Phirks/flip-card/kicad-pcb/RP2350_60QFN_minimal.kicad_sch

## KiCad design kicad-pcb/RP2350_60QFN_minimal.kicad_sch (2025-08-04)

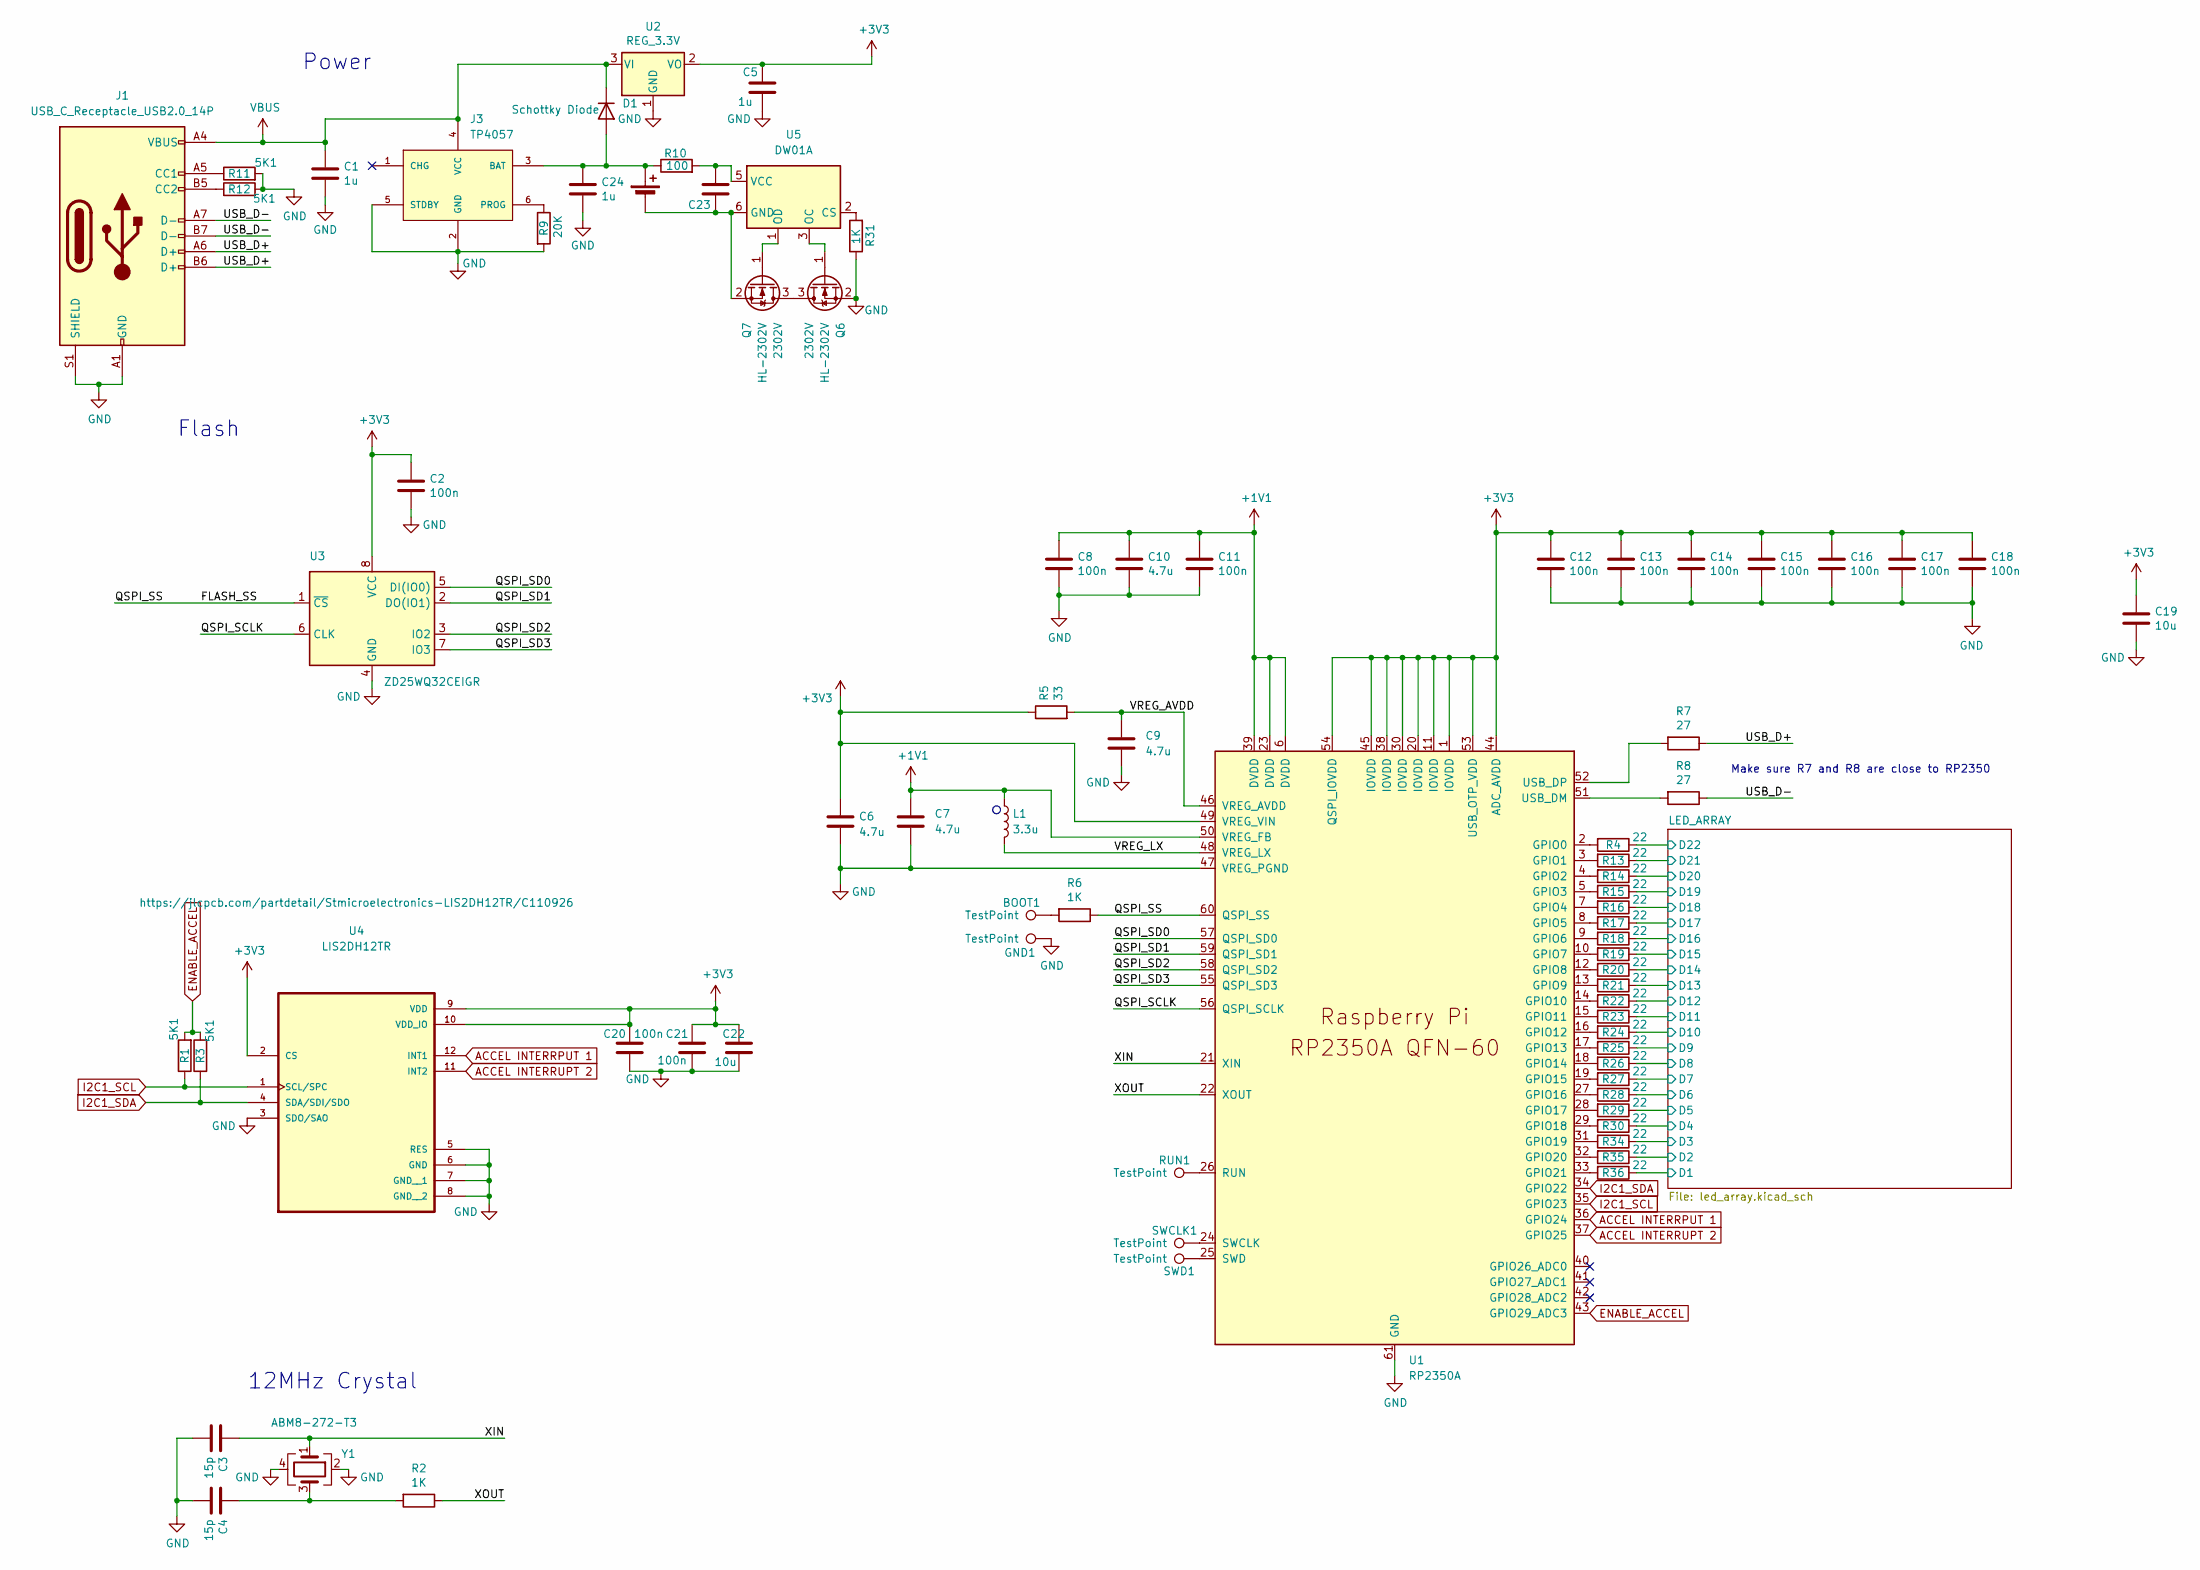
[picture p12: schematic RP2350_60QFN_minimal.kicad_sch]

Parts:
BOOT1: TestPoint; TestPoint_Pad_1.0x1.0mm
BT1: Battery_Cell; BatteryHolder_Custom; Part Number RJD2430C1ST1
C1, C5, C24: 1u; C_0402_1005Metric_small_pads; Part Number TCC0402X5R105M6R3AT
C2, C8, C11, C12, C13, C14, C15, C16, C17, C18, C20, C21, C23: 100n; C_0402_1005Metric_small_pads; Part Number FCC0402B104K160AT
C3, C4: 15p; C_0402_1005Metric_small_pads; Part Number CC0402FRNPO9BN150
C6, C7, C9, C10: 4.7u; C_0402_1005Metric_small_pads; Part Number TCC0402X5R475M6R3AT
C19, C22: 10u; C_0402_1005Metric_small_pads; Part Number GRM155R60J106ME44D
D1: Schottky Diode; D_SOD-323; Part Number CUS10S30,H3F; JLC Number C146335
GND1: TestPoint; TestPoint_Pad_1.0x1.0mm
J1: USB_C_Receptacle_USB2.0_14P; USB_C_PADDLE
J3: TP4057; SOT-23-6; Part Number TP4057; LCSC Part Number C497923
L1: 3.3u; L_pol_2016; Part Number AOTA-B201610S3R3-101-T
Q6, Q7: HL-2302V; SOT-23; Part Number 2302V; LCSC Part Number C7431443
R1, R3, R11, R12: 5K1; R_0402_1005Metric; Part Number 0402WGF510KTCE
R2, R6, R31: 1K; R_0402_1005Metric; Part Number FRC0402F1001TS
R4, R13, R14, R15, R16, R17, R18, R19, R20, R21, R22, R23, R24, R25, R26, R27, R28, R29, R30, R34, R35, R36: 22; R_0402_1005Metric; Part Number 0402WGF220JTCE
R5: 33; R_0402_1005Metric; Part Number RC0402FR-0733RL
R7, R8: 27; R_0402_1005Metric; Part Number 0402WGJ0100TCE
R9: 20K; R_0402_1005Metric; Part Number 0402WGF2002TCE
R10: 100; R_0402_1005Metric; Part Number FRC0402F1000TS
RUN1: TestPoint; TestPoint_Pad_1.0x1.0mm
SWCLK1: TestPoint; TestPoint_Pad_1.0x1.0mm
SWD1: TestPoint; TestPoint_Pad_1.0x1.0mm
U1: RP2350A; RP2350-QFN-60-1EP_7x7_P0.4mm_EP3.4x3.4mm_ThermalVias; Part Number RP2350A
U2: REG_3.3V; SOT-23; Part Number XC6206P332MR-MS
U3: ZD25WQ32CEIGR; Winbond_USON-8-1EP_3x2mm_P0.5mm_EP0.2x1.6mm; Part Number ZD25WQ32CEIGR
U4: LIS2DH12TR; LGA-12_2x2mm_P0.5mm; Part Number LIS2DH12TR
U5: DW01A; SOT-23-6; Part Number DW01A; LCSC Part Number C42380662
Y1: ABM8-272-T3; Crystal_SMD_3225-4Pin_3.2x2.5mm

Connections:
+1V1: C7.1, C8.1, C10.1, C11.1, L1.1, U1.6 (DVDD), U1.23 (DVDD), U1.39 (DVDD), U1.50 (VREG_FB)
+3V3: C2.1, C5.1, C6.1, C12.1, C13.1, C14.1, C15.1, C16.1, C17.1, C18.1, C19.1, C20.2, C21.2, C22.1, R5.1, U1.1 (IOVDD), U1.11 (IOVDD), U1.20 (IOVDD), U1.30 (IOVDD), U1.38 (IOVDD), U1.44 (ADC_AVDD), U1.45 (IOVDD), U1.49 (VREG_VIN), U1.53 (USB_OTP_VDD), U1.54 (QSPI_IOVDD), U2.2 (VO), U3.8 (VCC), U4.2 (CS), U4.9 (VDD), U4.10 (VDD_IO)
ACCEL INTERRPUT 1: U1.36 (GPIO24), U4.12 (INT1)
ACCEL INTERRUPT 2: U1.37 (GPIO25), U4.11 (INT2)
D1: R36.1
D2: R35.1
D3: R34.1
D4: R30.1
D5: R29.1
D6: R28.1
D7: R27.1
D8: R26.1
D9: R25.1
D10: R24.1
D11: R23.1
D12: R22.1
D13: R21.1
D14: R20.1
D15: R19.1
D16: R18.1
D17: R17.1
D18: R16.1
D19: R15.1
D20: R14.1
D21: R13.1
D22: R4.1
ENABLE_ACCEL: R1.2, R3.2, U1.43 (GPIO29_ADC3)
FLASH_SS: R6.1, U1.60 (QSPI_SS), U3.1 (~CS)
GND: C1.2, C2.2, C3.2, C4.2, C5.2, C6.2, C7.2, C8.2, C9.2, C10.2, C11.2, C12.2, C13.2, C14.2, C15.2, C16.2, C17.2, C18.2, C19.2, C20.1, C21.1, C22.2, C24.2, GND1.1, J1.A1 (GND), J1.A12 (GND), J1.B1 (GND), J1.B12 (GND), J1.S1 (SHIELD), J3.2 (GND), J3.5 (STDBY), Q6.2 (S), R9.2, R11.2, R12.2, R31.1, U1.47 (VREG_PGND), U1.61 (GND), U2.1 (GND), U3.4 (GND), U4.3 (SDO/SAO), U4.5 (RES), U4.6 (GND), U4.7 (GND__1), U4.8 (GND__2), Y1.2, Y1.4
I2C1_SCL: R1.1, U1.35 (GPIO23), U4.1 (SCL/SPC)
I2C1_SDA: R3.1, U1.34 (GPIO22), U4.4 (SDA/SDI/SDO)
unnamed: BOOT1.1, R6.2
unnamed: BT1.1 (+), C24.1, D1.2 (A), J3.3 (BAT), R10.1
unnamed: BT1.2 (-), C23.2, Q7.2 (S), U5.6 (GND)
unnamed: C4.1, R2.2, Y1.3
unnamed: C23.1, R10.2, U5.5 (VCC)
unnamed: J1.A5 (CC1), R11.1
unnamed: J1.B5 (CC2), R12.1
unnamed: J3.6 (PROG), R9.1
unnamed: Q6.1 (G), U5.3 (OC)
unnamed: Q6.3 (D), Q7.3 (D)
unnamed: Q7.1 (G), U5.1 (OD)
unnamed: R4.2, U1.2 (GPIO0)
unnamed: R7.2, U1.52 (USB_DP)
unnamed: R8.2, U1.51 (USB_DM)
unnamed: R13.2, U1.3 (GPIO1)
unnamed: R14.2, U1.4 (GPIO2)
unnamed: R15.2, U1.5 (GPIO3)
unnamed: R16.2, U1.7 (GPIO4)
unnamed: R17.2, U1.8 (GPIO5)
unnamed: R18.2, U1.9 (GPIO6)
unnamed: R19.2, U1.10 (GPIO7)
unnamed: R20.2, U1.12 (GPIO8)
unnamed: R21.2, U1.13 (GPIO9)
unnamed: R22.2, U1.14 (GPIO10)
unnamed: R23.2, U1.15 (GPIO11)
unnamed: R24.2, U1.16 (GPIO12)
unnamed: R25.2, U1.17 (GPIO13)
unnamed: R26.2, U1.18 (GPIO14)
unnamed: R27.2, U1.19 (GPIO15)
unnamed: R28.2, U1.27 (GPIO16)
unnamed: R29.2, U1.28 (GPIO17)
unnamed: R30.2, U1.29 (GPIO18)
unnamed: R31.2, U5.2 (CS)
unnamed: R34.2, U1.31 (GPIO19)
unnamed: R35.2, U1.32 (GPIO20)
unnamed: R36.2, U1.33 (GPIO21)
unnamed: RUN1.1, U1.26 (RUN)
unnamed: SWCLK1.1, U1.24 (SWCLK)
unnamed: SWD1.1, U1.25 (SWD)
QSPI_SCLK: U1.56 (QSPI_SCLK), U3.6 (CLK)
QSPI_SD0: U1.57 (QSPI_SD0), U3.5 (DI(IO0))
QSPI_SD1: U1.59 (QSPI_SD1), U3.2 (DO(IO1))
QSPI_SD2: U1.58 (QSPI_SD2), U3.3 (IO2)
QSPI_SD3: U1.55 (QSPI_SD3), U3.7 (IO3)
USB_D+: J1.A6 (D+), J1.B6 (D+), R7.1
USB_D-: J1.A7 (D-), J1.B7 (D-), R8.1
VBUS: C1.1, D1.1 (K), J1.A4 (VBUS), J1.A9 (VBUS), J1.B4 (VBUS), J1.B9 (VBUS), J3.4 (VCC), U2.3 (VI)
VREG_AVDD: C9.1, R5.2, U1.46 (VREG_AVDD)
VREG_LX: L1.2, U1.48 (VREG_LX)
XIN: C3.1, U1.21 (XIN), Y1.1
XOUT: R2.1, U1.22 (XOUT)

Notes on the sheet:
Flash
Make sure R7 and R8 are close to RP2350
12MHz Crystal
Power
