Phirks/flip-card/kicad-pcb/led_array.kicad_sch

## KiCad design kicad-pcb/led_array.kicad_sch (2025-08-04)

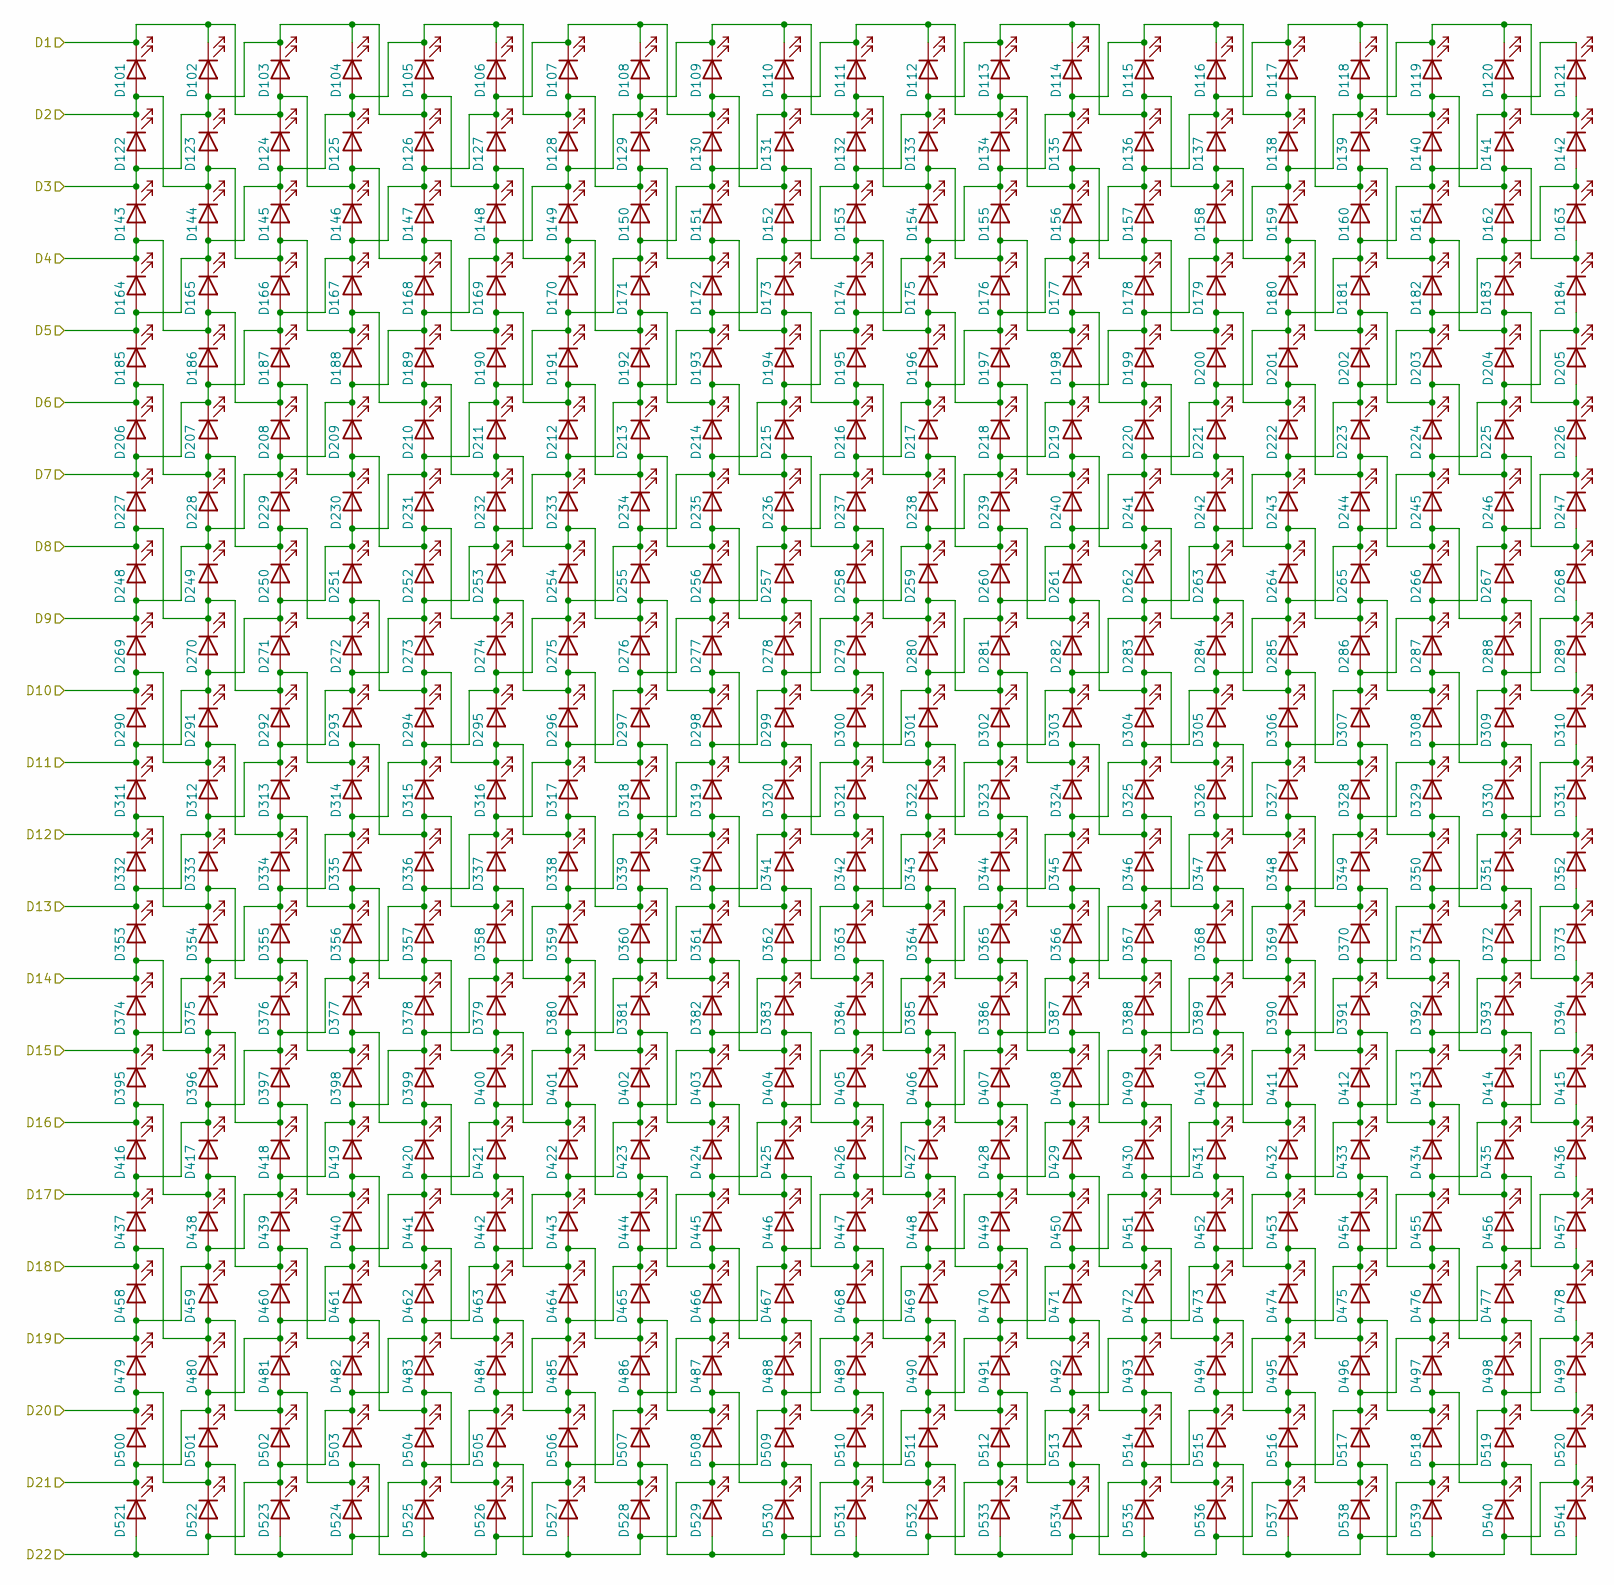
[picture p13: schematic led_array.kicad_sch]

Parts:
D101, D102, D103, D104, D105, D106, D107, D108, D109, D110, D111, D112, D113, D114, D115, D116, D117, D118, D119, D120, D121, D122, D123, D124, D125, D126, D127, D128, D129, D130, D131, D132, D133, D134, D135, D136, D137, D138, D139, D140, D141, D142, D143, D144, D145, D146, D147, D148, D149, D150, D151, D152, D153, D154, D155, D156, D157, D158, D159, D160, D161, D162, D163, D164, D165, D166, D167, D168, D169, D170, D171, D172, D173, D174, D175, D176, D177, D178, D179, D180, D181, D182, D183, D184, D185, D186, D187, D188, D189, D190, D191, D192, D193, D194, D195, D196, D197, D198, D199, D200, D201, D202, D203, D204, D205, D206, D207, D208, D209, D210, D211, D212, D213, D214, D215, D216, D217, D218, D219, D220, D221, D222, D223, D224, D225, D226, D227, D228, D229, D230, D231, D232, D233, D234, D235, D236, D237, D238, D239, D240, D241, D242, D243, D244, D245, D246, D247, D248, D249, D250, D251, D252, D253, D254, D255, D256, D257, D258, D259, D260, D261, D262, D263, D264, D265, D266, D267, D268, D269, D270, D271, D272, D273, D274, D275, D276, D277, D278, D279, D280, D281, D282, D283, D284, D285, D286, D287, D288, D289, D290, D291, D292, D293, D294, D295, D296, D297, D298, D299, D300, D301, D302, D303, D304, D305, D306, D307, D308, D309, D310, D311, D312, D313, D314, D315, D316, D317, D318, D319, D320, D321, D322, D323, D324, D325, D326, D327, D328, D329, D330, D331, D332, D333, D334, D335, D336, D337, D338, D339, D340, D341, D342, D343, D344, D345, D346, D347, D348, D349, D350, D351, D352, D353, D354, D355, D356, D357, D358, D359, D360, D361, D362, D363, D364, D365, D366, D367, D368, D369, D370, D371, D372, D373, D374, D375, D376, D377, D378, D379, D380, D381, D382, D383, D384, D385, D386, D387, D388, D389, D390, D391, D392, D393, D394, D395, D396, D397, D398, D399, D400, D401, D402, D403, D404, D405, D406, D407, D408, D409, D410, D411, D412, D413, D414, D415, D416, D417, D418, D419, D420, D421, D422, D423, D424, D425, D426, D427, D428, D429, D430, D431, D432, D433, D434, D435, D436, D437, D438, D439, D440, D441, D442, D443, D444, D445, D446, D447, D448, D449, D450, D451, D452, D453, D454, D455, D456, D457, D458, D459, D460, D461, D462, D463, D464, D465, D466, D467, D468, D469, D470, D471, D472, D473, D474, D475, D476, D477, D478, D479, D480, D481, D482, D483, D484, D485, D486, D487, D488, D489, D490, D491, D492, D493, D494, D495, D496, D497, D498, D499, D500, D501, D502, D503, D504, D505, D506, D507, D508, D509, D510, D511, D512, D513, D514, D515, D516, D517, D518, D519, D520, D521, D522, D523, D524, D525, D526, D527, D528, D529, D530, D531, D532, D533, D534, D535, D536, D537, D538, D539, D540, D541: LED; LED_0603_1608Metric; Part Number HL-PT-1608H322W-L(6000K-7000K)

Connections:
D1: D101.1 (K), D102.1 (K), D103.2 (A), D124.1 (K), D125.2 (A), D146.1 (K), D147.2 (A), D168.1 (K), D169.2 (A), D190.1 (K), D191.2 (A), D212.1 (K), D213.2 (A), D234.1 (K), D235.2 (A), D256.1 (K), D257.2 (A), D278.1 (K), D279.2 (A), D300.1 (K), D301.2 (A), D322.1 (K), D323.2 (A), D344.1 (K), D345.2 (A), D366.1 (K), D367.2 (A), D388.1 (K), D389.2 (A), D410.1 (K), D411.2 (A), D432.1 (K), D433.2 (A), D454.1 (K), D455.2 (A), D476.1 (K), D477.2 (A), D498.1 (K), D499.2 (A), D520.1 (K)
D2: D101.2 (A), D122.1 (K), D123.2 (A), D144.1 (K), D145.2 (A), D166.1 (K), D167.2 (A), D188.1 (K), D189.2 (A), D210.1 (K), D211.2 (A), D232.1 (K), D233.2 (A), D254.1 (K), D255.2 (A), D276.1 (K), D277.2 (A), D298.1 (K), D299.2 (A), D320.1 (K), D321.2 (A), D342.1 (K), D343.2 (A), D364.1 (K), D365.2 (A), D386.1 (K), D387.2 (A), D408.1 (K), D409.2 (A), D430.1 (K), D431.2 (A), D452.1 (K), D453.2 (A), D474.1 (K), D475.2 (A), D496.1 (K), D497.2 (A), D518.1 (K), D519.2 (A), D540.1 (K), D541.2 (A)
D3: D102.2 (A), D103.1 (K), D104.1 (K), D105.2 (A), D122.2 (A), D123.1 (K), D126.1 (K), D127.2 (A), D143.1 (K), D148.1 (K), D149.2 (A), D170.1 (K), D171.2 (A), D192.1 (K), D193.2 (A), D214.1 (K), D215.2 (A), D236.1 (K), D237.2 (A), D258.1 (K), D259.2 (A), D280.1 (K), D281.2 (A), D302.1 (K), D303.2 (A), D324.1 (K), D325.2 (A), D346.1 (K), D347.2 (A), D368.1 (K), D369.2 (A), D390.1 (K), D391.2 (A), D412.1 (K), D413.2 (A), D434.1 (K), D435.2 (A), D456.1 (K), D457.2 (A), D478.1 (K)
D4: D143.2 (A), D164.1 (K), D165.2 (A), D186.1 (K), D187.2 (A), D208.1 (K), D209.2 (A), D230.1 (K), D231.2 (A), D252.1 (K), D253.2 (A), D274.1 (K), D275.2 (A), D296.1 (K), D297.2 (A), D318.1 (K), D319.2 (A), D340.1 (K), D341.2 (A), D362.1 (K), D363.2 (A), D384.1 (K), D385.2 (A), D406.1 (K), D407.2 (A), D428.1 (K), D429.2 (A), D450.1 (K), D451.2 (A), D472.1 (K), D473.2 (A), D494.1 (K), D495.2 (A), D516.1 (K), D517.2 (A), D520.2 (A), D538.1 (K), D539.2 (A), D540.2 (A), D541.1 (K)
D5: D104.2 (A), D105.1 (K), D106.1 (K), D107.2 (A), D124.2 (A), D125.1 (K), D128.1 (K), D129.2 (A), D144.2 (A), D145.1 (K), D150.1 (K), D151.2 (A), D164.2 (A), D165.1 (K), D172.1 (K), D173.2 (A), D185.1 (K), D194.1 (K), D195.2 (A), D216.1 (K), D217.2 (A), D238.1 (K), D239.2 (A), D260.1 (K), D261.2 (A), D282.1 (K), D283.2 (A), D304.1 (K), D305.2 (A), D326.1 (K), D327.2 (A), D348.1 (K), D349.2 (A), D370.1 (K), D371.2 (A), D392.1 (K), D393.2 (A), D414.1 (K), D415.2 (A), D436.1 (K)
D6: D185.2 (A), D206.1 (K), D207.2 (A), D228.1 (K), D229.2 (A), D250.1 (K), D251.2 (A), D272.1 (K), D273.2 (A), D294.1 (K), D295.2 (A), D316.1 (K), D317.2 (A), D338.1 (K), D339.2 (A), D360.1 (K), D361.2 (A), D382.1 (K), D383.2 (A), D404.1 (K), D405.2 (A), D426.1 (K), D427.2 (A), D448.1 (K), D449.2 (A), D470.1 (K), D471.2 (A), D478.2 (A), D492.1 (K), D493.2 (A), D498.2 (A), D499.1 (K), D514.1 (K), D515.2 (A), D518.2 (A), D519.1 (K), D536.1 (K), D537.2 (A), D538.2 (A), D539.1 (K)
D7: D106.2 (A), D107.1 (K), D108.1 (K), D109.2 (A), D126.2 (A), D127.1 (K), D130.1 (K), D131.2 (A), D146.2 (A), D147.1 (K), D152.1 (K), D153.2 (A), D166.2 (A), D167.1 (K), D174.1 (K), D175.2 (A), D186.2 (A), D187.1 (K), D196.1 (K), D197.2 (A), D206.2 (A), D207.1 (K), D218.1 (K), D219.2 (A), D227.1 (K), D240.1 (K), D241.2 (A), D262.1 (K), D263.2 (A), D284.1 (K), D285.2 (A), D306.1 (K), D307.2 (A), D328.1 (K), D329.2 (A), D350.1 (K), D351.2 (A), D372.1 (K), D373.2 (A), D394.1 (K)
D8: D227.2 (A), D248.1 (K), D249.2 (A), D270.1 (K), D271.2 (A), D292.1 (K), D293.2 (A), D314.1 (K), D315.2 (A), D336.1 (K), D337.2 (A), D358.1 (K), D359.2 (A), D380.1 (K), D381.2 (A), D402.1 (K), D403.2 (A), D424.1 (K), D425.2 (A), D436.2 (A), D446.1 (K), D447.2 (A), D456.2 (A), D457.1 (K), D468.1 (K), D469.2 (A), D476.2 (A), D477.1 (K), D490.1 (K), D491.2 (A), D496.2 (A), D497.1 (K), D512.1 (K), D513.2 (A), D516.2 (A), D517.1 (K), D534.1 (K), D535.2 (A), D536.2 (A), D537.1 (K)
D9: D108.2 (A), D109.1 (K), D110.1 (K), D111.2 (A), D128.2 (A), D129.1 (K), D132.1 (K), D133.2 (A), D148.2 (A), D149.1 (K), D154.1 (K), D155.2 (A), D168.2 (A), D169.1 (K), D176.1 (K), D177.2 (A), D188.2 (A), D189.1 (K), D198.1 (K), D199.2 (A), D208.2 (A), D209.1 (K), D220.1 (K), D221.2 (A), D228.2 (A), D229.1 (K), D242.1 (K), D243.2 (A), D248.2 (A), D249.1 (K), D264.1 (K), D265.2 (A), D269.1 (K), D286.1 (K), D287.2 (A), D308.1 (K), D309.2 (A), D330.1 (K), D331.2 (A), D352.1 (K)
D10: D269.2 (A), D290.1 (K), D291.2 (A), D312.1 (K), D313.2 (A), D334.1 (K), D335.2 (A), D356.1 (K), D357.2 (A), D378.1 (K), D379.2 (A), D394.2 (A), D400.1 (K), D401.2 (A), D414.2 (A), D415.1 (K), D422.1 (K), D423.2 (A), D434.2 (A), D435.1 (K), D444.1 (K), D445.2 (A), D454.2 (A), D455.1 (K), D466.1 (K), D467.2 (A), D474.2 (A), D475.1 (K), D488.1 (K), D489.2 (A), D494.2 (A), D495.1 (K), D510.1 (K), D511.2 (A), D514.2 (A), D515.1 (K), D532.1 (K), D533.2 (A), D534.2 (A), D535.1 (K)
D11: D110.2 (A), D111.1 (K), D112.1 (K), D113.2 (A), D130.2 (A), D131.1 (K), D134.1 (K), D135.2 (A), D150.2 (A), D151.1 (K), D156.1 (K), D157.2 (A), D170.2 (A), D171.1 (K), D178.1 (K), D179.2 (A), D190.2 (A), D191.1 (K), D200.1 (K), D201.2 (A), D210.2 (A), D211.1 (K), D222.1 (K), D223.2 (A), D230.2 (A), D231.1 (K), D244.1 (K), D245.2 (A), D250.2 (A), D251.1 (K), D266.1 (K), D267.2 (A), D270.2 (A), D271.1 (K), D288.1 (K), D289.2 (A), D290.2 (A), D291.1 (K), D310.1 (K), D311.1 (K)
D12: D311.2 (A), D332.1 (K), D333.2 (A), D352.2 (A), D354.1 (K), D355.2 (A), D372.2 (A), D373.1 (K), D376.1 (K), D377.2 (A), D392.2 (A), D393.1 (K), D398.1 (K), D399.2 (A), D412.2 (A), D413.1 (K), D420.1 (K), D421.2 (A), D432.2 (A), D433.1 (K), D442.1 (K), D443.2 (A), D452.2 (A), D453.1 (K), D464.1 (K), D465.2 (A), D472.2 (A), D473.1 (K), D486.1 (K), D487.2 (A), D492.2 (A), D493.1 (K), D508.1 (K), D509.2 (A), D512.2 (A), D513.1 (K), D530.1 (K), D531.2 (A), D532.2 (A), D533.1 (K)
D13: D112.2 (A), D113.1 (K), D114.1 (K), D115.2 (A), D132.2 (A), D133.1 (K), D136.1 (K), D137.2 (A), D152.2 (A), D153.1 (K), D158.1 (K), D159.2 (A), D172.2 (A), D173.1 (K), D180.1 (K), D181.2 (A), D192.2 (A), D193.1 (K), D202.1 (K), D203.2 (A), D212.2 (A), D213.1 (K), D224.1 (K), D225.2 (A), D232.2 (A), D233.1 (K), D246.1 (K), D247.2 (A), D252.2 (A), D253.1 (K), D268.1 (K), D272.2 (A), D273.1 (K), D292.2 (A), D293.1 (K), D312.2 (A), D313.1 (K), D332.2 (A), D333.1 (K), D353.1 (K)
D14: D310.2 (A), D330.2 (A), D331.1 (K), D350.2 (A), D351.1 (K), D353.2 (A), D370.2 (A), D371.1 (K), D374.1 (K), D375.2 (A), D390.2 (A), D391.1 (K), D396.1 (K), D397.2 (A), D410.2 (A), D411.1 (K), D418.1 (K), D419.2 (A), D430.2 (A), D431.1 (K), D440.1 (K), D441.2 (A), D450.2 (A), D451.1 (K), D462.1 (K), D463.2 (A), D470.2 (A), D471.1 (K), D484.1 (K), D485.2 (A), D490.2 (A), D491.1 (K), D506.1 (K), D507.2 (A), D510.2 (A), D511.1 (K), D528.1 (K), D529.2 (A), D530.2 (A), D531.1 (K)
D15: D114.2 (A), D115.1 (K), D116.1 (K), D117.2 (A), D134.2 (A), D135.1 (K), D138.1 (K), D139.2 (A), D154.2 (A), D155.1 (K), D160.1 (K), D161.2 (A), D174.2 (A), D175.1 (K), D182.1 (K), D183.2 (A), D194.2 (A), D195.1 (K), D204.1 (K), D205.2 (A), D214.2 (A), D215.1 (K), D226.1 (K), D234.2 (A), D235.1 (K), D254.2 (A), D255.1 (K), D274.2 (A), D275.1 (K), D294.2 (A), D295.1 (K), D314.2 (A), D315.1 (K), D334.2 (A), D335.1 (K), D354.2 (A), D355.1 (K), D374.2 (A), D375.1 (K), D395.1 (K)
D16: D268.2 (A), D288.2 (A), D289.1 (K), D308.2 (A), D309.1 (K), D328.2 (A), D329.1 (K), D348.2 (A), D349.1 (K), D368.2 (A), D369.1 (K), D388.2 (A), D389.1 (K), D395.2 (A), D408.2 (A), D409.1 (K), D416.1 (K), D417.2 (A), D428.2 (A), D429.1 (K), D438.1 (K), D439.2 (A), D448.2 (A), D449.1 (K), D460.1 (K), D461.2 (A), D468.2 (A), D469.1 (K), D482.1 (K), D483.2 (A), D488.2 (A), D489.1 (K), D504.1 (K), D505.2 (A), D508.2 (A), D509.1 (K), D526.1 (K), D527.2 (A), D528.2 (A), D529.1 (K)
D17: D116.2 (A), D117.1 (K), D118.1 (K), D119.2 (A), D136.2 (A), D137.1 (K), D140.1 (K), D141.2 (A), D156.2 (A), D157.1 (K), D162.1 (K), D163.2 (A), D176.2 (A), D177.1 (K), D184.1 (K), D196.2 (A), D197.1 (K), D216.2 (A), D217.1 (K), D236.2 (A), D237.1 (K), D256.2 (A), D257.1 (K), D276.2 (A), D277.1 (K), D296.2 (A), D297.1 (K), D316.2 (A), D317.1 (K), D336.2 (A), D337.1 (K), D356.2 (A), D357.1 (K), D376.2 (A), D377.1 (K), D396.2 (A), D397.1 (K), D416.2 (A), D417.1 (K), D437.1 (K)
D18: D226.2 (A), D246.2 (A), D247.1 (K), D266.2 (A), D267.1 (K), D286.2 (A), D287.1 (K), D306.2 (A), D307.1 (K), D326.2 (A), D327.1 (K), D346.2 (A), D347.1 (K), D366.2 (A), D367.1 (K), D386.2 (A), D387.1 (K), D406.2 (A), D407.1 (K), D426.2 (A), D427.1 (K), D437.2 (A), D446.2 (A), D447.1 (K), D458.1 (K), D459.2 (A), D466.2 (A), D467.1 (K), D480.1 (K), D481.2 (A), D486.2 (A), D487.1 (K), D502.1 (K), D503.2 (A), D506.2 (A), D507.1 (K), D524.1 (K), D525.2 (A), D526.2 (A), D527.1 (K)
D19: D118.2 (A), D119.1 (K), D120.1 (K), D121.2 (A), D138.2 (A), D139.1 (K), D142.1 (K), D158.2 (A), D159.1 (K), D178.2 (A), D179.1 (K), D198.2 (A), D199.1 (K), D218.2 (A), D219.1 (K), D238.2 (A), D239.1 (K), D258.2 (A), D259.1 (K), D278.2 (A), D279.1 (K), D298.2 (A), D299.1 (K), D318.2 (A), D319.1 (K), D338.2 (A), D339.1 (K), D358.2 (A), D359.1 (K), D378.2 (A), D379.1 (K), D398.2 (A), D399.1 (K), D418.2 (A), D419.1 (K), D438.2 (A), D439.1 (K), D458.2 (A), D459.1 (K), D479.1 (K)
D20: D184.2 (A), D204.2 (A), D205.1 (K), D224.2 (A), D225.1 (K), D244.2 (A), D245.1 (K), D264.2 (A), D265.1 (K), D284.2 (A), D285.1 (K), D304.2 (A), D305.1 (K), D324.2 (A), D325.1 (K), D344.2 (A), D345.1 (K), D364.2 (A), D365.1 (K), D384.2 (A), D385.1 (K), D404.2 (A), D405.1 (K), D424.2 (A), D425.1 (K), D444.2 (A), D445.1 (K), D464.2 (A), D465.1 (K), D479.2 (A), D484.2 (A), D485.1 (K), D500.1 (K), D501.2 (A), D504.2 (A), D505.1 (K), D522.1 (K), D523.2 (A), D524.2 (A), D525.1 (K)
D21: D120.2 (A), D121.1 (K), D140.2 (A), D141.1 (K), D160.2 (A), D161.1 (K), D180.2 (A), D181.1 (K), D200.2 (A), D201.1 (K), D220.2 (A), D221.1 (K), D240.2 (A), D241.1 (K), D260.2 (A), D261.1 (K), D280.2 (A), D281.1 (K), D300.2 (A), D301.1 (K), D320.2 (A), D321.1 (K), D340.2 (A), D341.1 (K), D360.2 (A), D361.1 (K), D380.2 (A), D381.1 (K), D400.2 (A), D401.1 (K), D420.2 (A), D421.1 (K), D440.2 (A), D441.1 (K), D460.2 (A), D461.1 (K), D480.2 (A), D481.1 (K), D500.2 (A), D501.1 (K), D521.1 (K)
D22: D142.2 (A), D162.2 (A), D163.1 (K), D182.2 (A), D183.1 (K), D202.2 (A), D203.1 (K), D222.2 (A), D223.1 (K), D242.2 (A), D243.1 (K), D262.2 (A), D263.1 (K), D282.2 (A), D283.1 (K), D302.2 (A), D303.1 (K), D322.2 (A), D323.1 (K), D342.2 (A), D343.1 (K), D362.2 (A), D363.1 (K), D382.2 (A), D383.1 (K), D402.2 (A), D403.1 (K), D422.2 (A), D423.1 (K), D442.2 (A), D443.1 (K), D462.2 (A), D463.1 (K), D482.2 (A), D483.1 (K), D502.2 (A), D503.1 (K), D521.2 (A), D522.2 (A), D523.1 (K)
